jc2409/Smart_Guitar_Amp/data/images/breadboard.jpeg

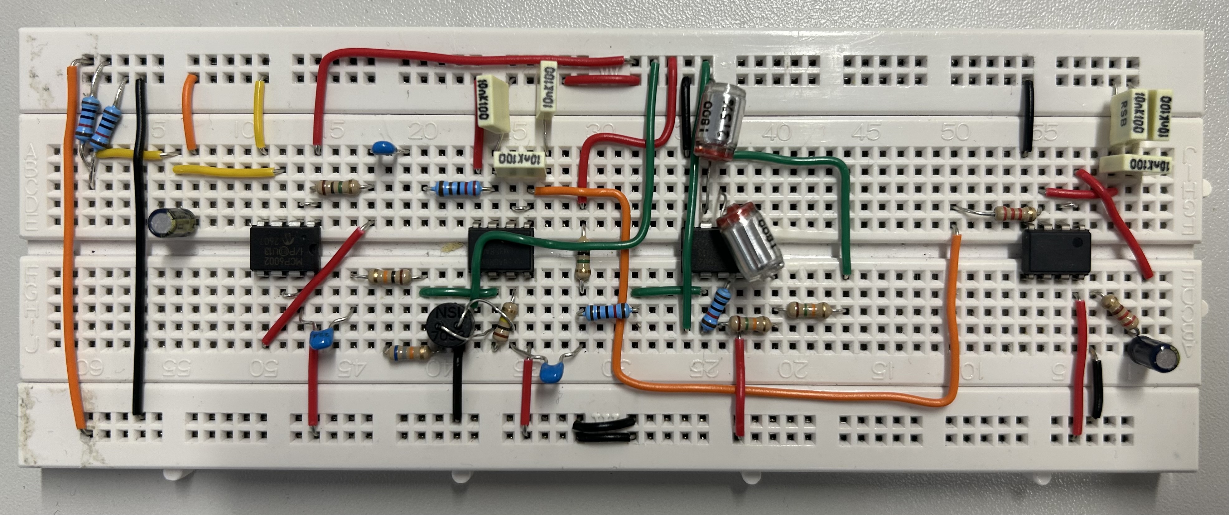
data/images/breadboard.jpeg
