jc2409/Smart_Guitar_Amp/data/images/ui_tuner.png

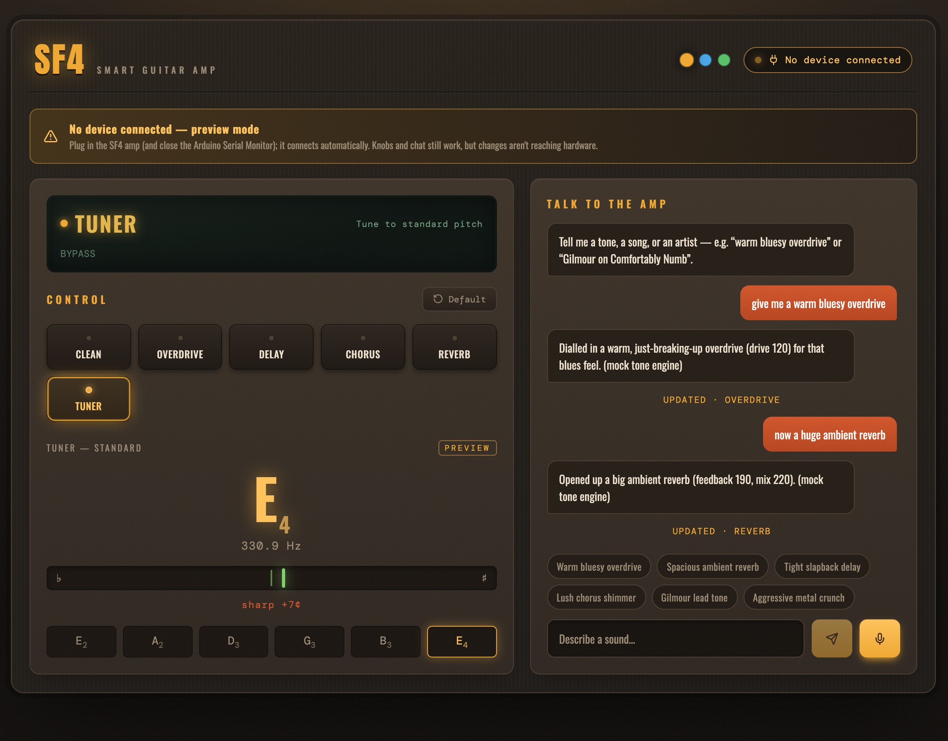
data/images/ui_tuner.png
