jc2409/Smart_Guitar_Amp/data/images/audio_output_stage_simulation.png

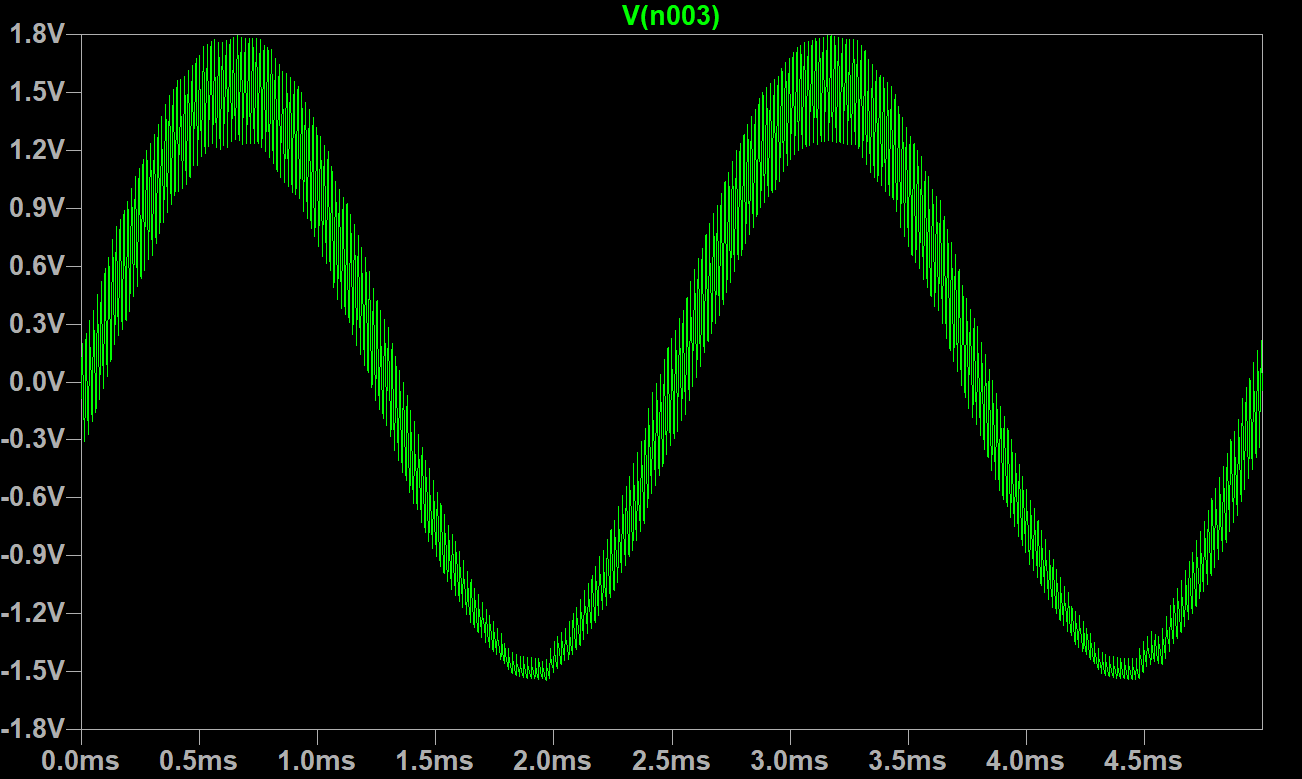
data/images/audio_output_stage_simulation.png
