jc2409/Smart_Guitar_Amp/data/images/demo_rig.jpeg

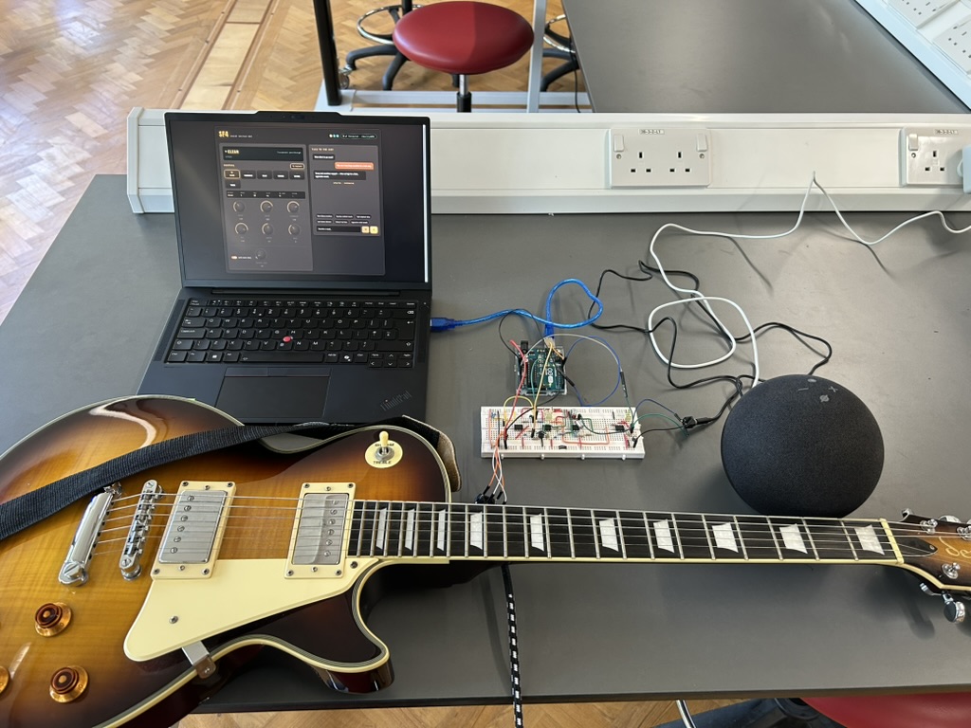
data/images/demo_rig.jpeg
