jc2409/Smart_Guitar_Amp/data/images/filter_schematic.png

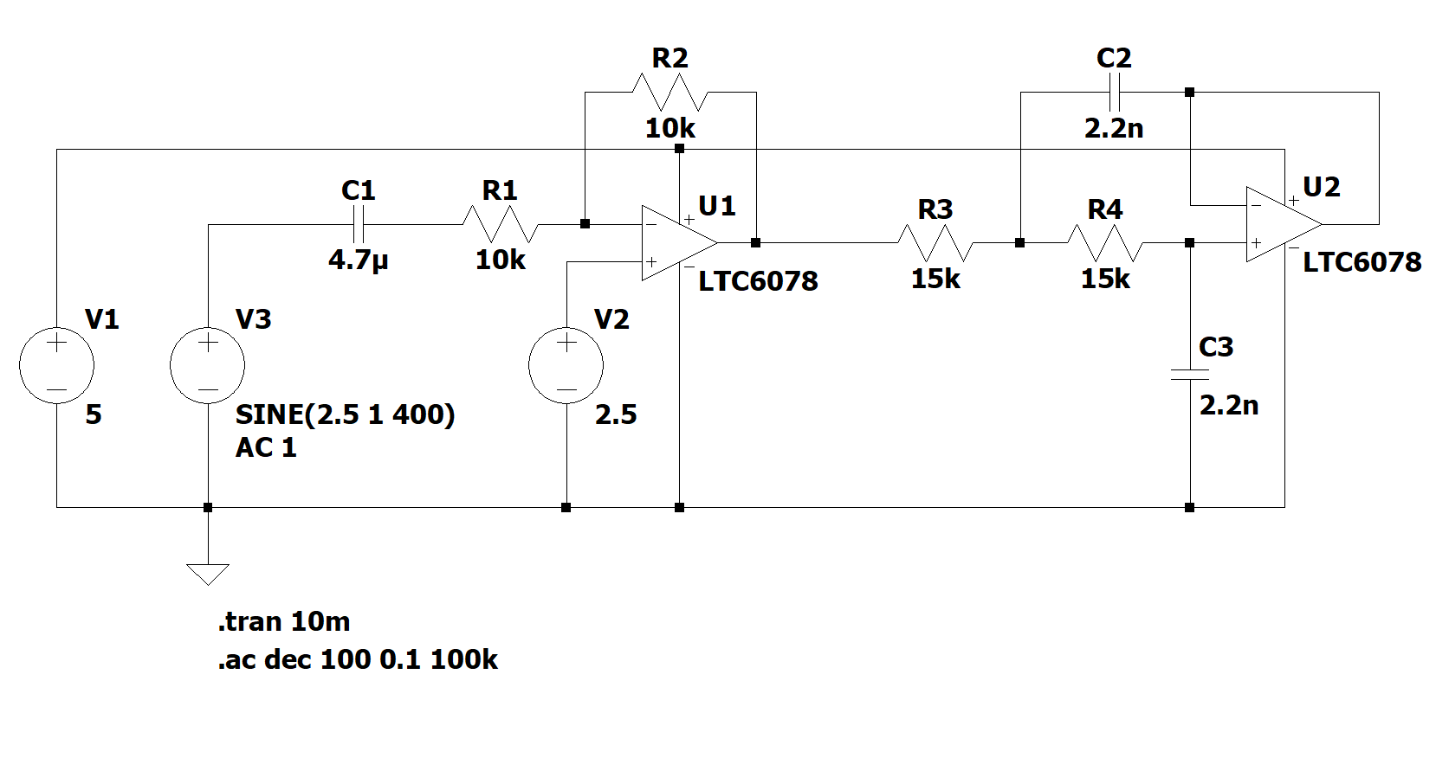
data/images/filter_schematic.png
