jc2409/Smart_Guitar_Amp/data/images/filter_simulation.png

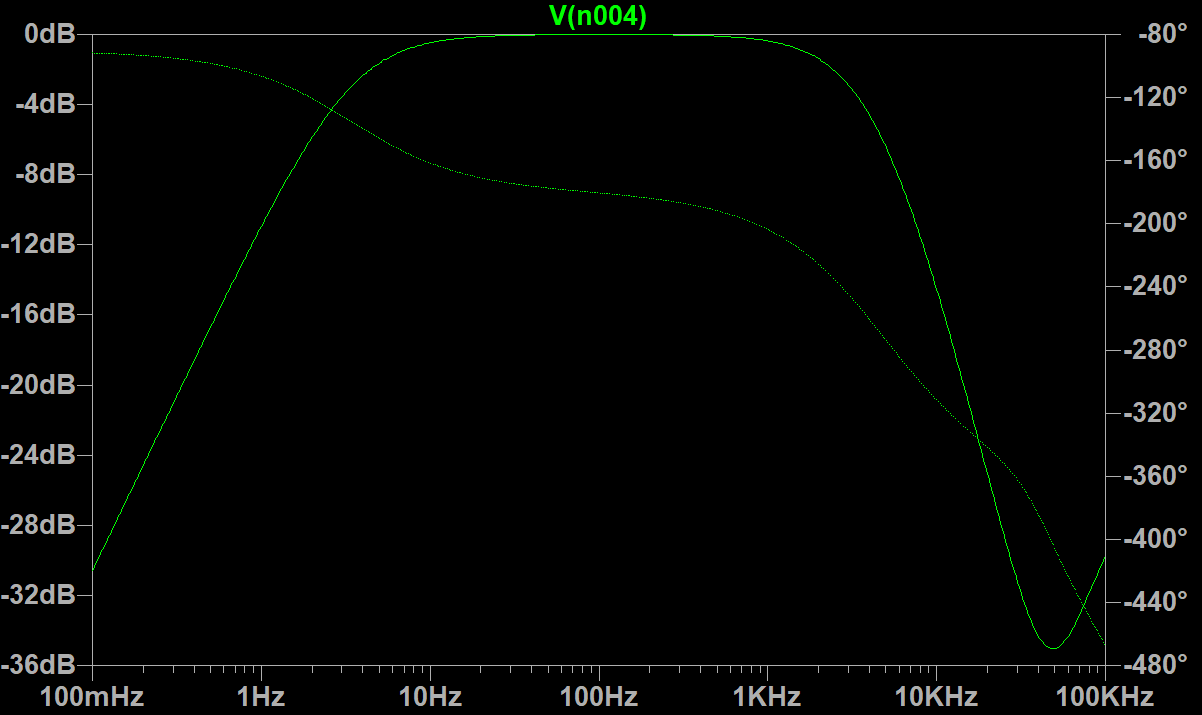
data/images/filter_simulation.png
