jc2409/Smart_Guitar_Amp/data/images/firmware_software_flow.png

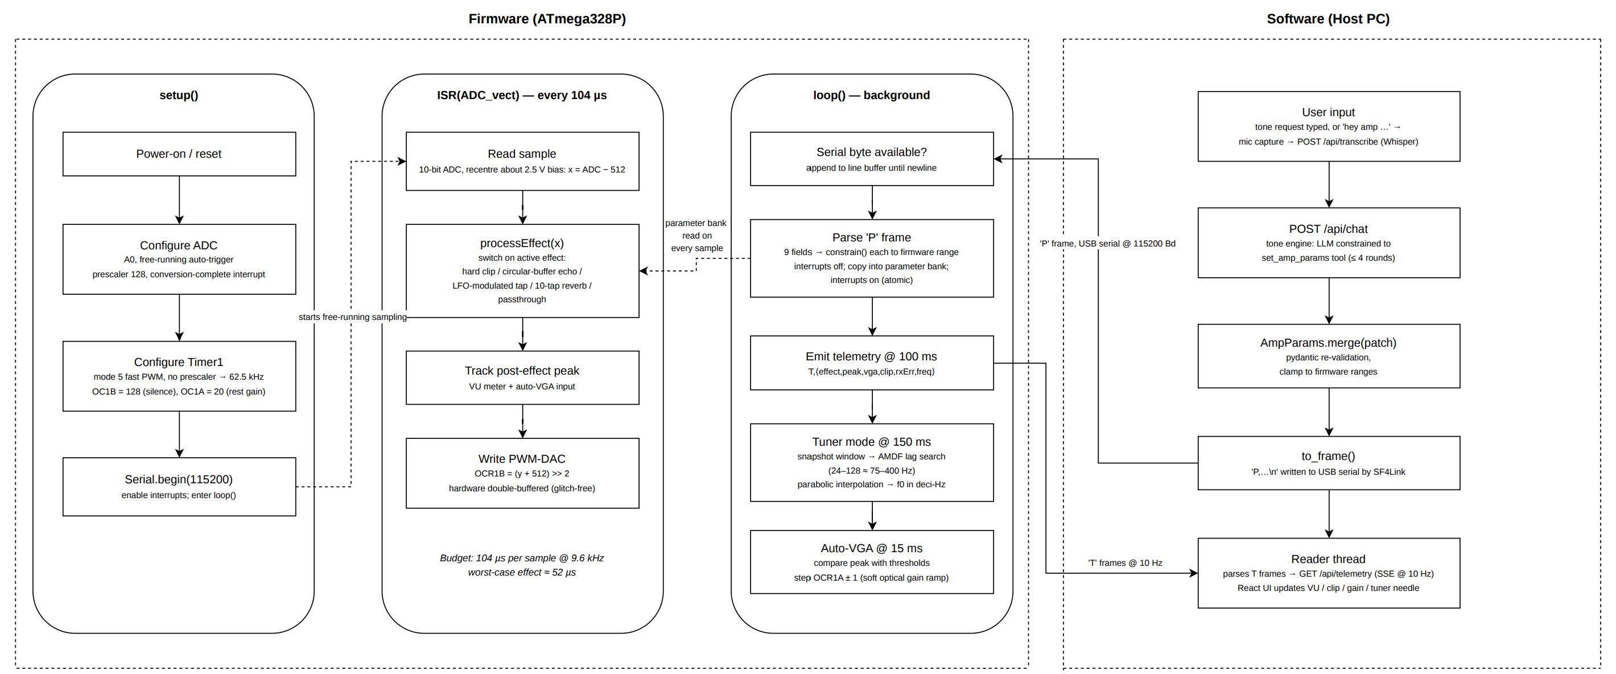
data/images/firmware_software_flow.png
