jc2409/Smart_Guitar_Amp/data/images/full_circuit_schematic.png

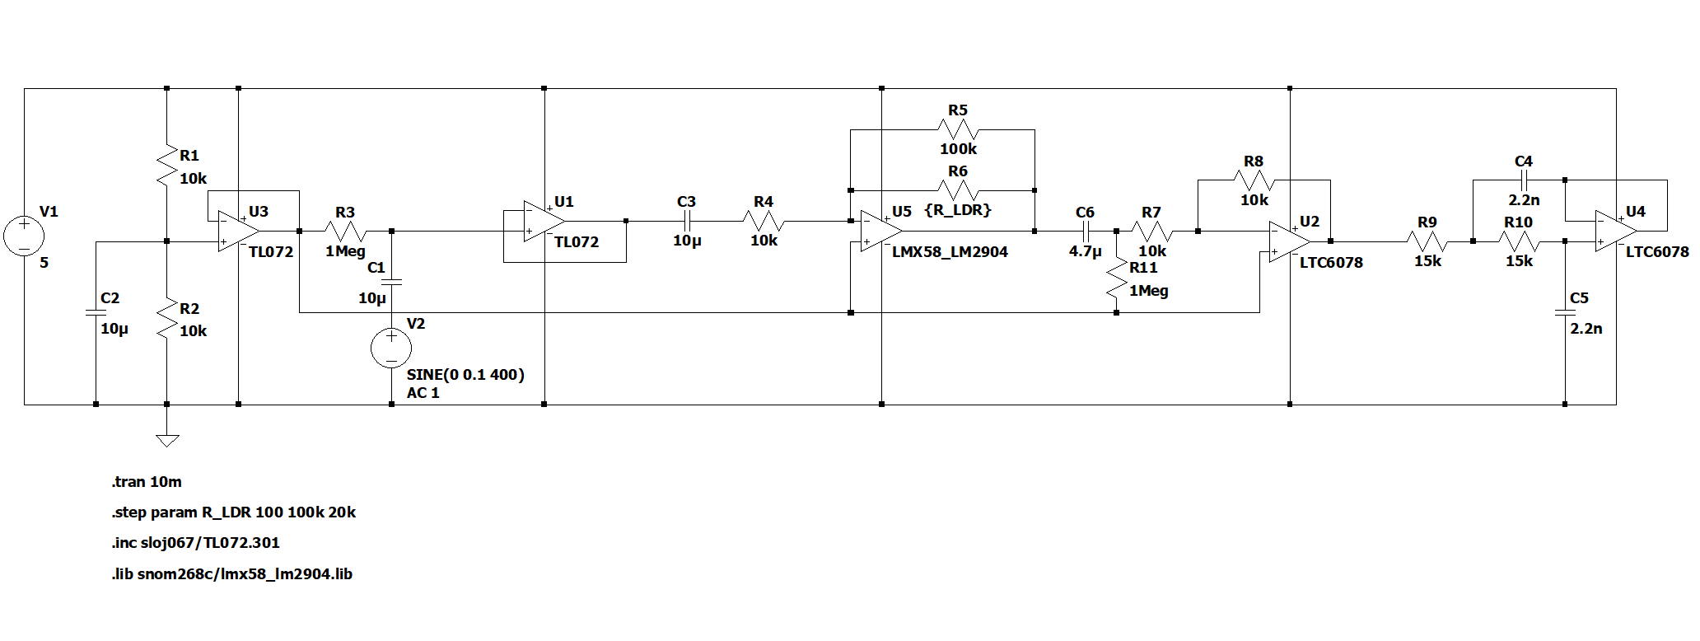
data/images/full_circuit_schematic.png
