jc2409/Smart_Guitar_Amp/data/images/input_buffer_schematic.png

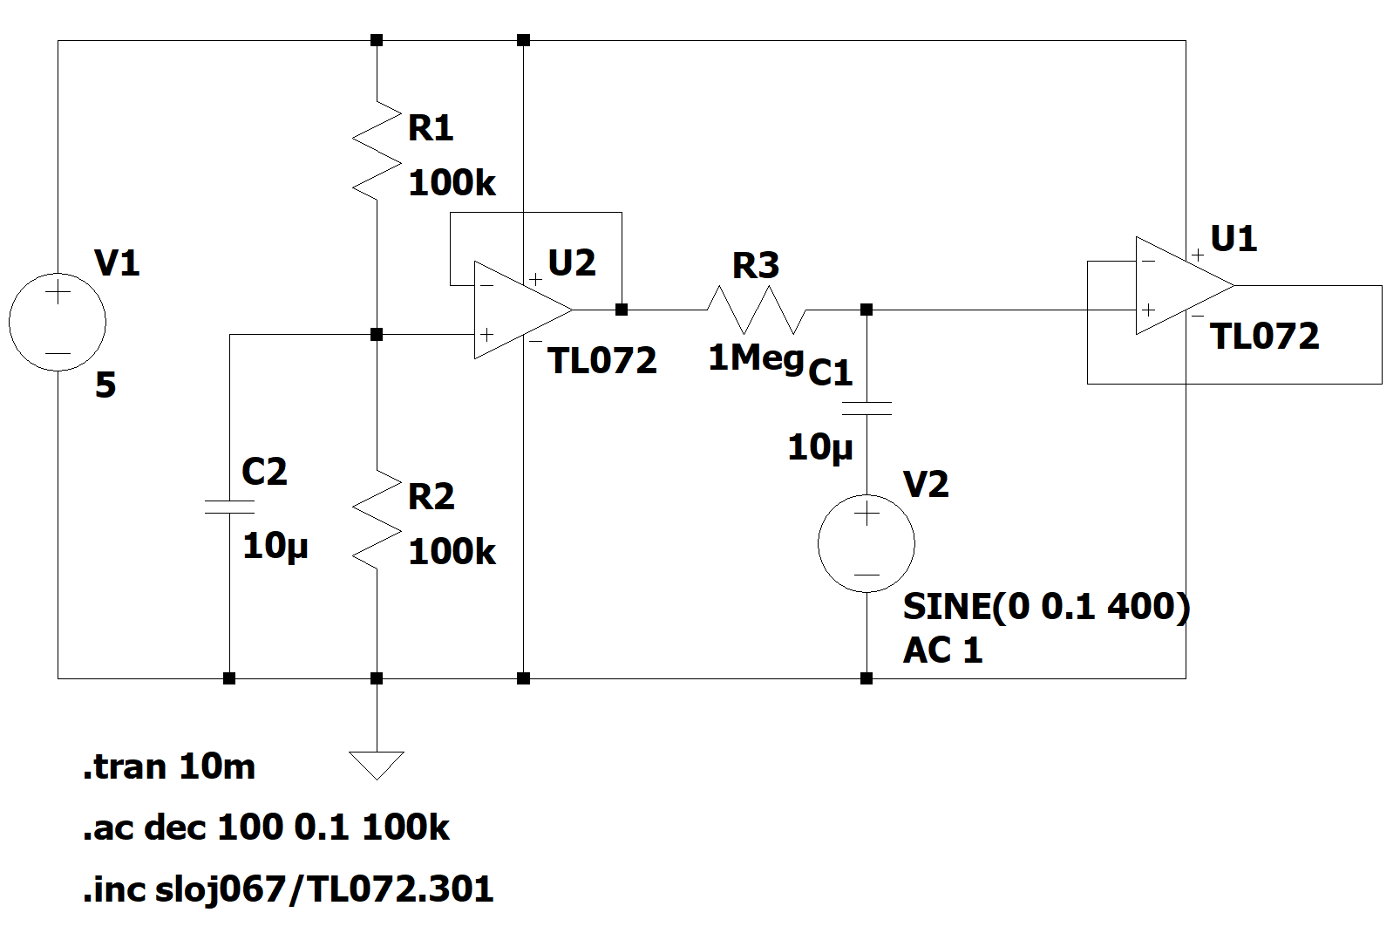
data/images/input_buffer_schematic.png
