jc2409/Smart_Guitar_Amp/data/images/input_buffer_tran_simulation.png

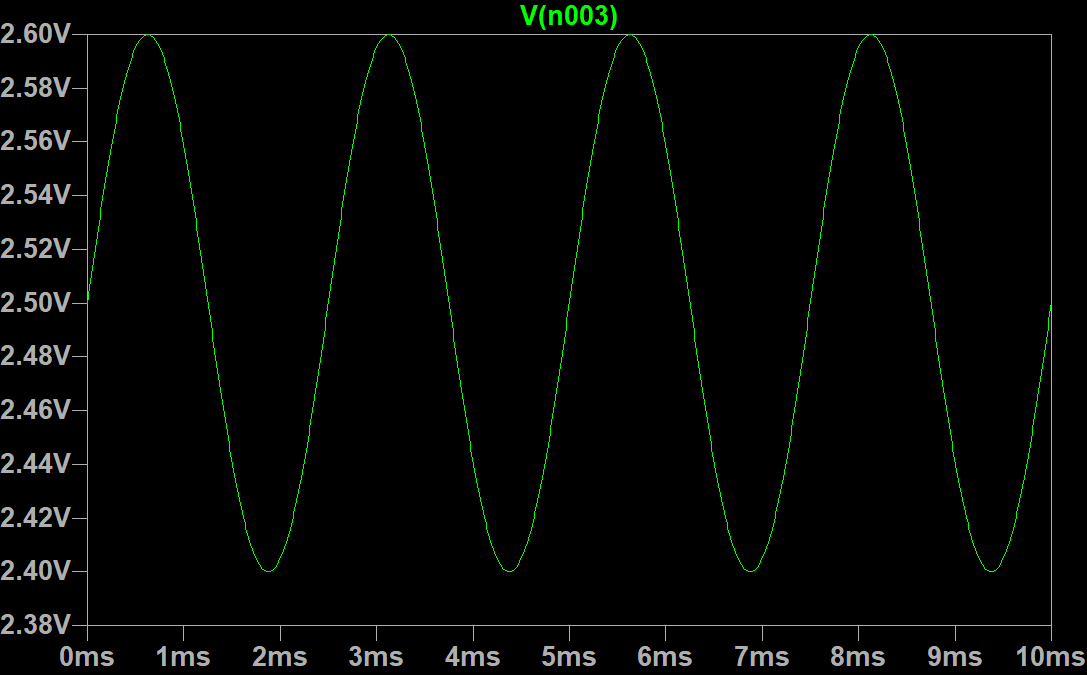
data/images/input_buffer_tran_simulation.png
