jc2409/Smart_Guitar_Amp/data/images/schematic.png

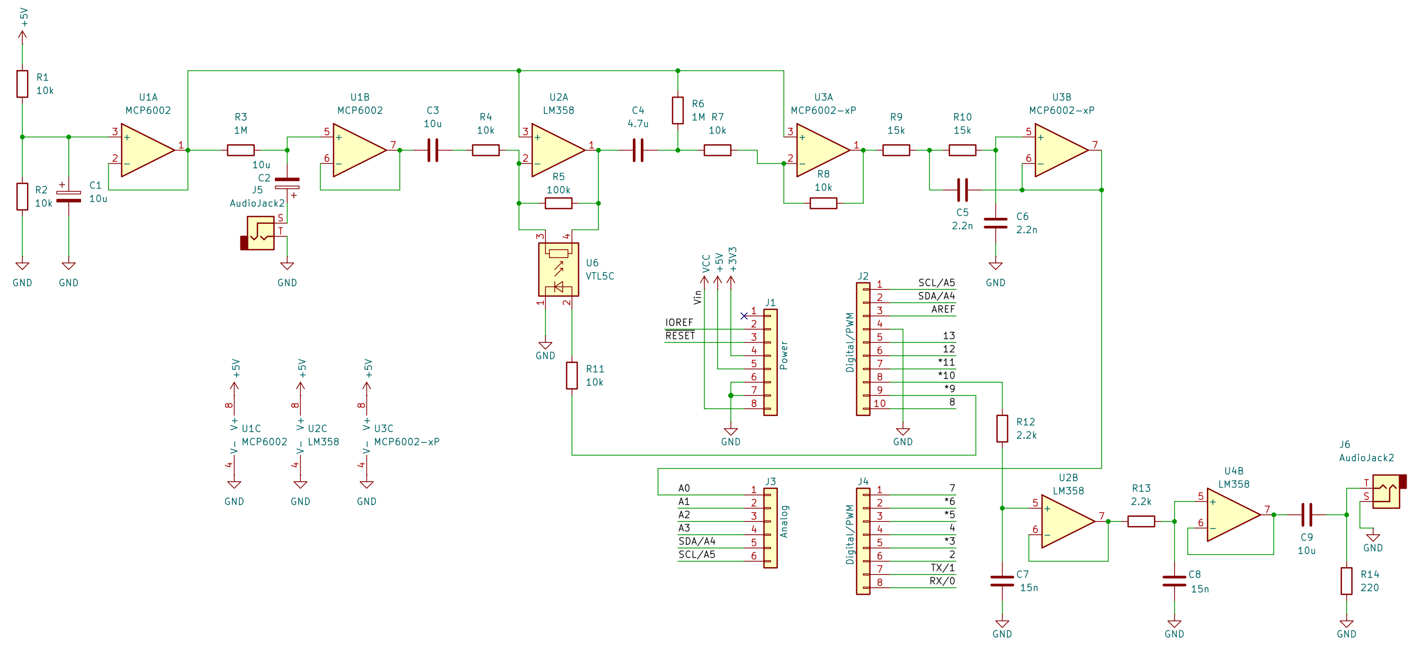
data/images/schematic.png
