jc2409/Smart_Guitar_Amp/data/images/software_stack.png

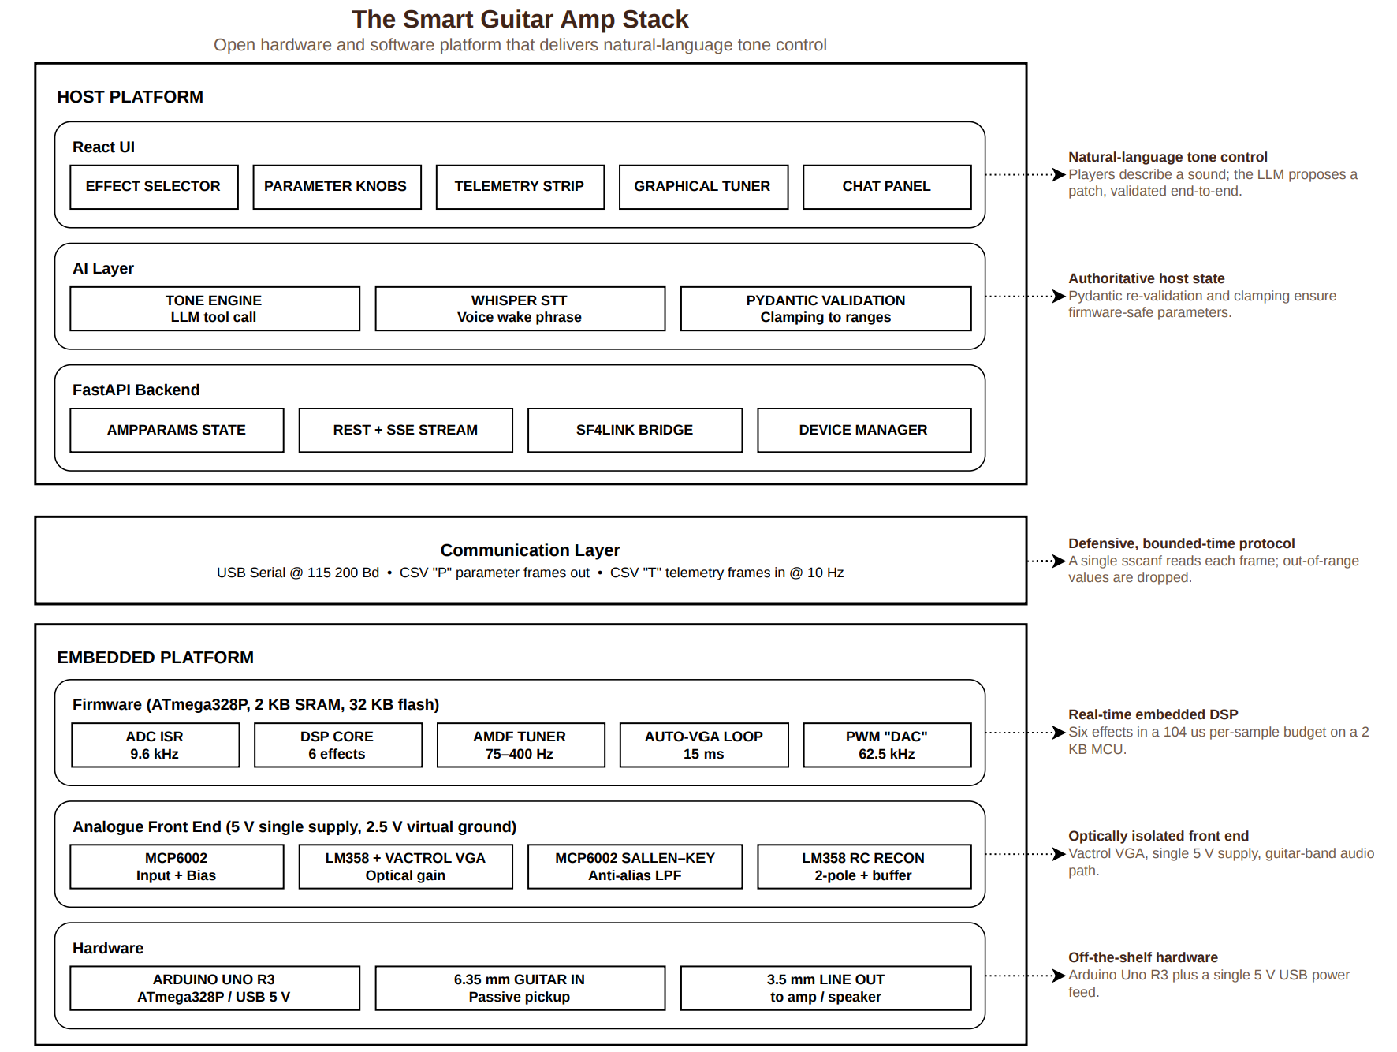
data/images/software_stack.png
