jc2409/Smart_Guitar_Amp/data/images/systems_comms.png

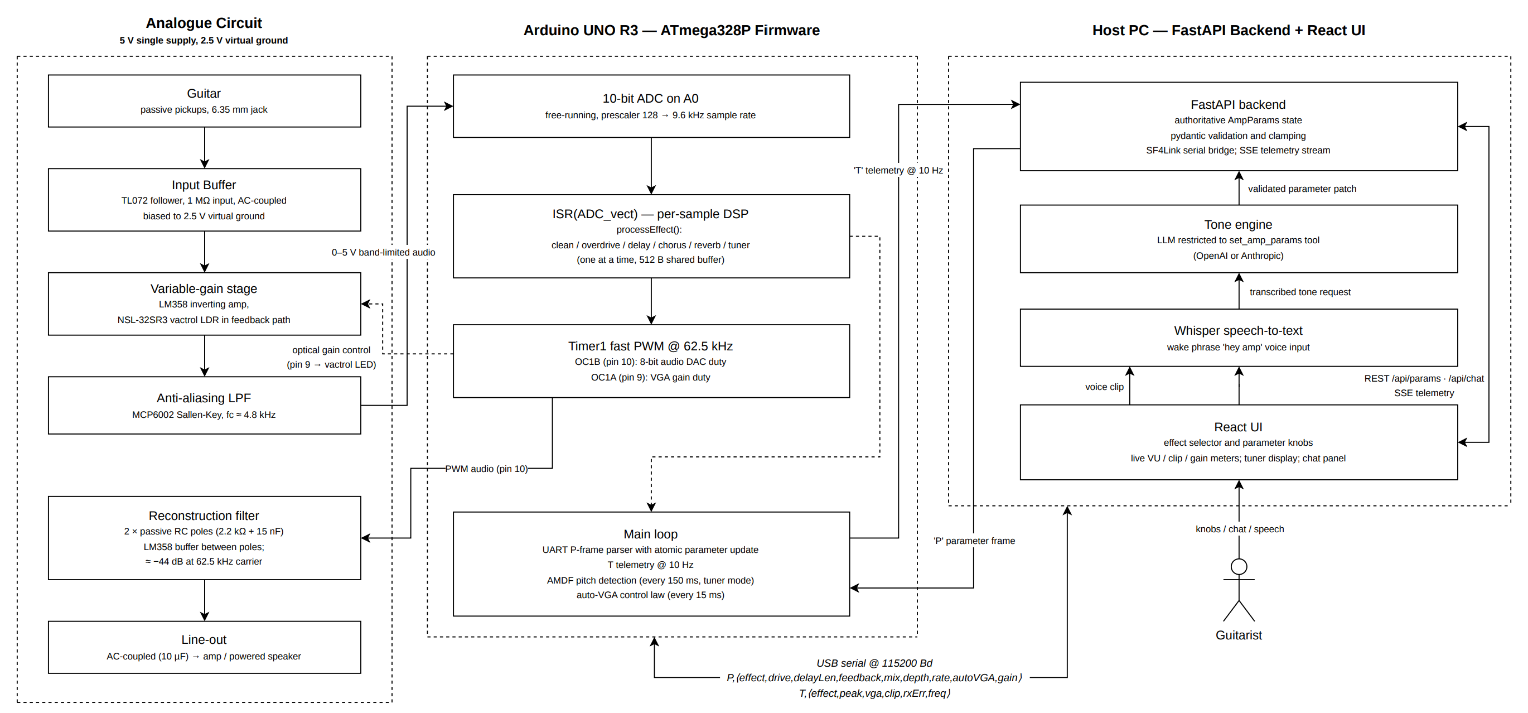
data/images/systems_comms.png
