jc2409/Smart_Guitar_Amp/data/images/ui_chat_reverb.png

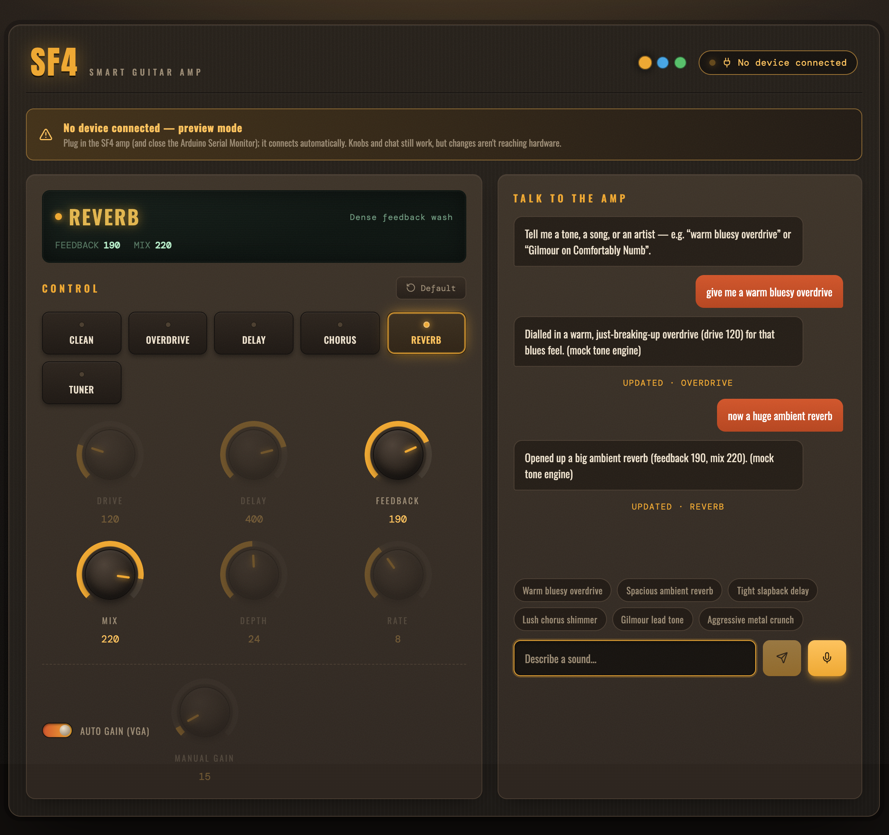
data/images/ui_chat_reverb.png
