jc2409/Smart_Guitar_Amp/data/images/vga_schematic.png

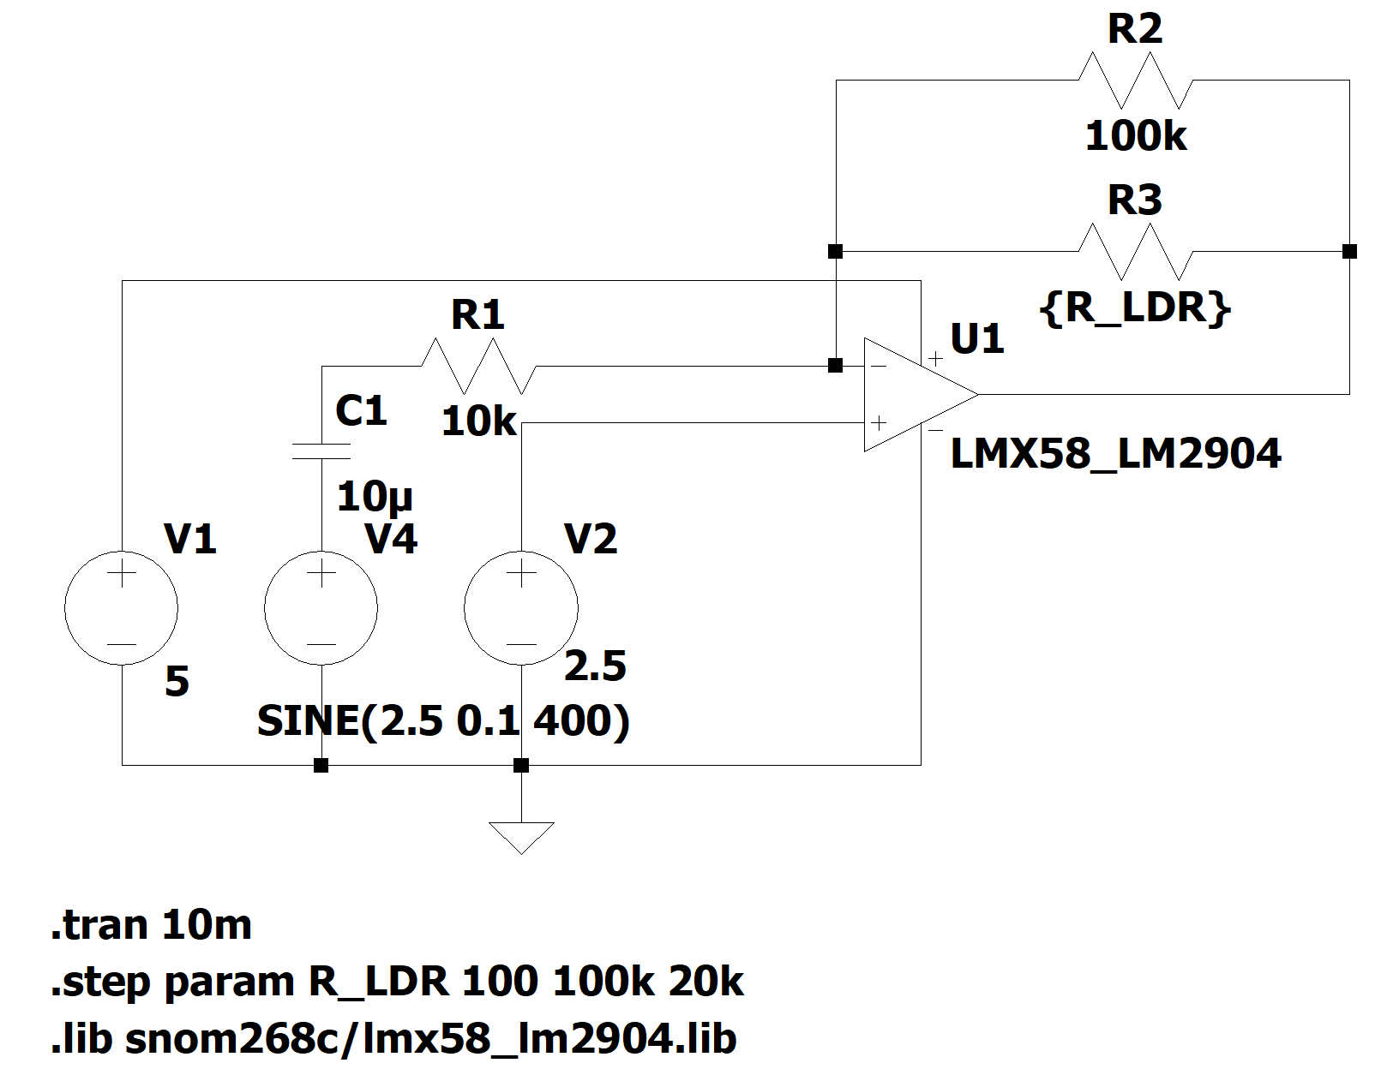
data/images/vga_schematic.png
