jc2409/Smart_Guitar_Amp/data/images/vga_simulation.png

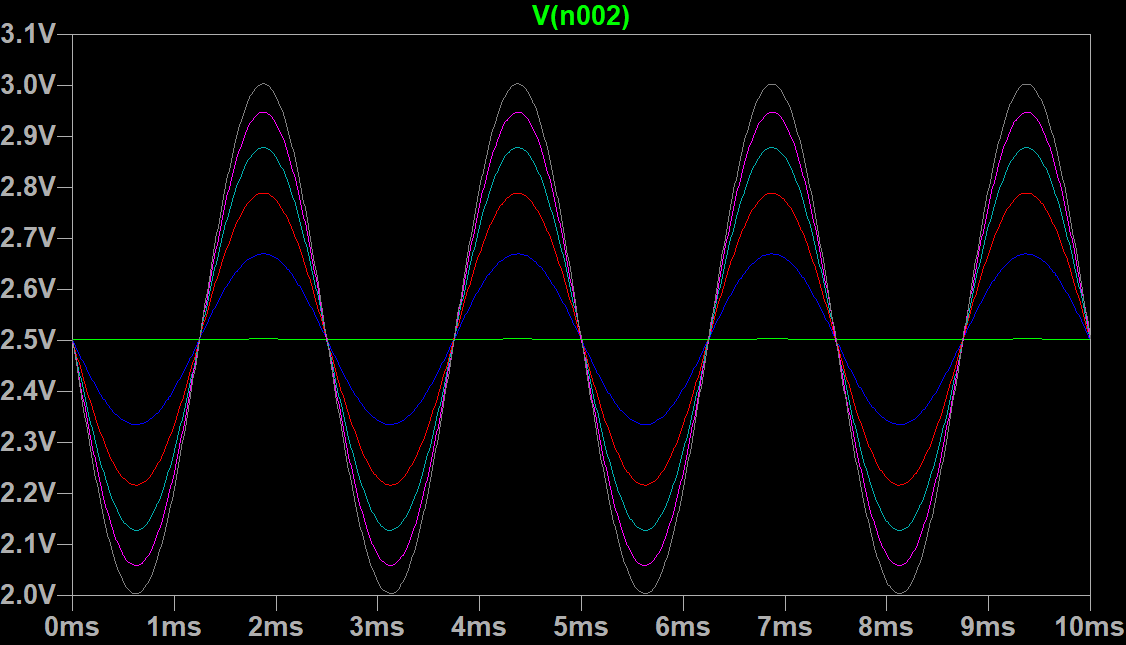
data/images/vga_simulation.png
