jc2409/Smart_Guitar_Amp/data/schematics/LTSpice/input_buffer.asc

C1: cap; 10�
C2: cap; 10�
R1: res; 100k
R2: res; 100k
R3: res; 1Meg
U1: opamp2; TL072
U2: opamp2; TL072
V1: voltage; 5
V2: voltage; SINE(0 0.1 400); AC 1
Named nets: 0
.tran 10m
.ac dec 100 0.1 100k
.inc sloj067/TL072.301
