jc2409/Smart_Guitar_Amp/data/schematics/LTSpice/variable_gain_amplifier.asc

C1: cap; 10µ
R1: res; 10k
R2: res; 100k
R3: res; {R_LDR}
U1: opamp2; LMX58_LM2904
V1: voltage; 5
V2: voltage; 2.5
V4: voltage; SINE(2.5 0.1 400)
Named nets: 0
.tran 10m
.step param R_LDR 100 100k 20k
.lib snom268c/lmx58_lm2904.lib
