jc2409/Smart_Guitar_Amp/data/schematics/LTSpice/MCP6001.asc

C1: cap; 4.7µ
C2: cap; 2.2n
C3: cap; 2.2n
R1: res; 10k
R2: res; 10k
R3: res; 15k
R4: res; 15k
U1: opamp2; MCP6002
U2: opamp2; MCP6002
V1: voltage; 5
V2: voltage; 2.5
V3: voltage; SINE(2.5 1 400); AC 1
Named nets: 0
.include MCP6002.txt
.tran 10m
